mlab-modules/SOLARMINIBAT01/doc/src/img/IMG_20220821_234056.jpg

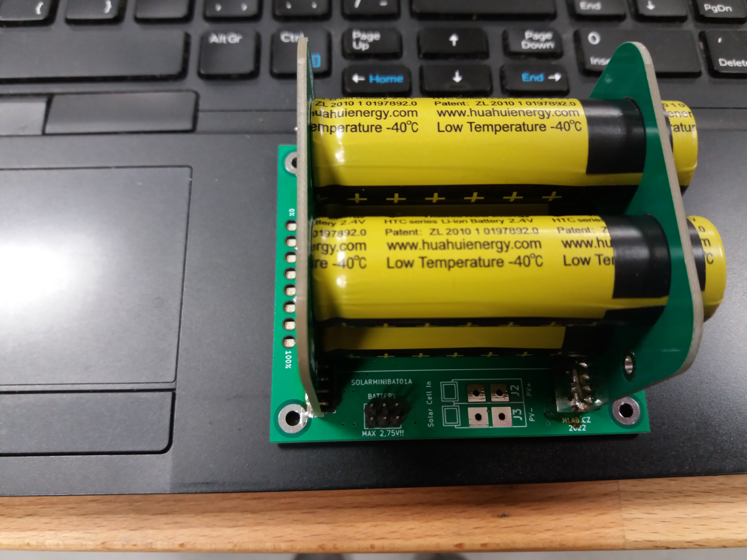
doc/src/img/IMG_20220821_234056.jpg
