mlab-modules/SOLARMINIBAT01/doc/gen/dxf/SOLARMINIBAT01A-F_Courtyard.dxf

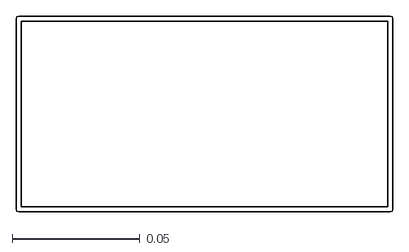
[picture p14: CAD file, 2022-08-10]
doc/gen/dxf/SOLARMINIBAT01A-F_Courtyard.dxf
0.148 x 0.0768
