mlab-modules/SOLARMINIBAT01/doc/gen/dxf/SOLARMINIBAT01A-Edge_Cuts.dxf

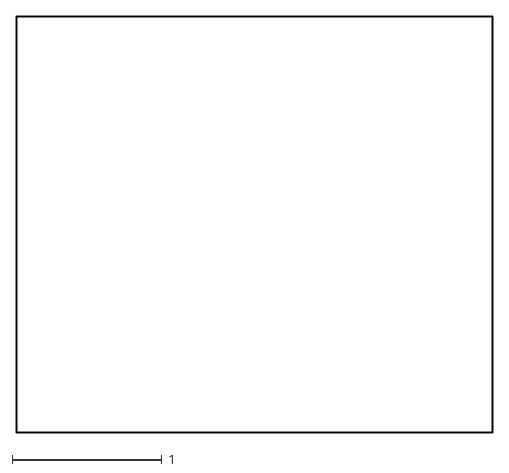
[picture p15: CAD file, 2022-08-10]
doc/gen/dxf/SOLARMINIBAT01A-Edge_Cuts.dxf
3.18 x 2.78
